Nilvero/SysWbud1/src/MainMenu.h

/*
 * MainMenu.h
 *
 *  Created on: May 6, 2016
 *      Author: krzys
 */
#include "stm32f429i_discovery_lcd.h"
#include "Button.h"
#include "stm32f429i_discovery_ioe.h"
#include "Chart.h"
#include "ChartsMenu.h"
#include "Results.h"

#ifndef MAINMENU_H_
#define MAINMENU_H_

void LCDinit(void);

void MainMenu();

#endif /* MAINMENU_H_ */
