Nilvero/SysWbud1/src/DS1337.c

/*
 * DS1337.c
 *
 *  Created on: Apr 30, 2016
 *      Author: krzys
 */
#include "DS1337.h"
#include "SharedFunctions.h"

void ds1337_INIT(){
	if(I2C3_CONFIGURED==0){
		InitI2C2();
	}
}
void ds1337_writeRecordToRegister(uint8_t adress,uint8_t value){
	// enable auto-ACK
	I2C_AcknowledgeConfig(I2C2,ENABLE);
	I2C_GenerateSTOP(I2C2,DISABLE);

	// generate start condition
	I2C_GenerateSTART(I2C2,ENABLE);
	while(!I2C_CheckEvent(I2C2,I2C_EVENT_MASTER_MODE_SELECT)){}

	// sent RTC adress
	I2C_Send7bitAddress(I2C2,DS1337_ADRESS<<1,I2C_Direction_Transmitter);
	while(!I2C_CheckEvent(I2C2,I2C_EVENT_MASTER_TRANSMITTER_MODE_SELECTED)){}

	// sent register ID adress
	I2C_SendData(I2C2,adress);
	while(I2C_CheckEvent(I2C2,I2C_EVENT_MASTER_BYTE_TRANSMITTING)!=SUCCESS){}

	// sent data to selected register
	I2C_SendData(I2C2,value);
	while(I2C_CheckEvent(I2C2,I2C_EVENT_MASTER_BYTE_TRANSMITTING)!=SUCCESS){}
	I2C_GenerateSTOP(I2C2,ENABLE);

}

void ds1337_writeRecordsToRegisters(uint8_t beginAdress,uint8_t * array,uint8_t size){
	// enable auto-ACK
	I2C_AcknowledgeConfig(I2C2,ENABLE);
	I2C_GenerateSTOP(I2C2,DISABLE);

	// generate start condition
	I2C_GenerateSTART(I2C2,ENABLE);
	while(!I2C_CheckEvent(I2C2,I2C_EVENT_MASTER_MODE_SELECT)){}

	// sent RTC adress
	I2C_Send7bitAddress(I2C2,DS1337_ADRESS<<1,I2C_Direction_Transmitter);
	while(!I2C_CheckEvent(I2C2,I2C_EVENT_MASTER_TRANSMITTER_MODE_SELECTED)){}

	// sent begin ID of writing register (auto-increment as default)
	I2C_SendData(I2C2,beginAdress);
	while(I2C_CheckEvent(I2C2,I2C_EVENT_MASTER_BYTE_TRANSMITTING)!=SUCCESS){}

	// write buffer to RTC
	uint8_t loopCounter=0;
	for(;loopCounter<size;loopCounter++){
		I2C_SendData(I2C2,array[loopCounter]);
		while(I2C_CheckEvent(I2C2,I2C_EVENT_MASTER_BYTE_TRANSMITTING)!=SUCCESS){}
	}
	// generate STOP condition
	I2C_GenerateSTOP(I2C2,ENABLE);
}

void ds1337_readRecordsFromRegisters(uint8_t beginAdress,uint8_t * array,uint8_t size){
	// wait for free line
	while(I2C_GetFlagStatus(I2C2, I2C_FLAG_BUSY)){}

	// generate start condition
	I2C_GenerateSTART(I2C2,ENABLE);
	while(!I2C_CheckEvent(I2C2,I2C_EVENT_MASTER_MODE_SELECT)){}

	// sent RTC adress
	I2C_Send7bitAddress(I2C2,DS1337_ADRESS<<1,I2C_Direction_Transmitter);
	while(!I2C_CheckEvent(I2C2,I2C_EVENT_MASTER_TRANSMITTER_MODE_SELECTED)){}

	// sent adress of first first reading register (auto-increment as default)
	I2C_SendData(I2C2,beginAdress);
	while(I2C_CheckEvent(I2C2,I2C_EVENT_MASTER_BYTE_TRANSMITTING)!=SUCCESS){}

	// generate stop
	I2C_GenerateSTART(I2C2,ENABLE);
	while(I2C_CheckEvent(I2C2,I2C_EVENT_MASTER_MODE_SELECT)!=SUCCESS){}

	// enable auto-acknowledge
	I2C_AcknowledgeConfig(I2C2,ENABLE);
	I2C_GenerateSTOP(I2C2,DISABLE);

	// sent RTC adress
	I2C_Send7bitAddress(I2C2,DS1337_ADRESS<<1,I2C_Direction_Receiver);
	while(I2C_CheckEvent(I2C2,I2C_EVENT_MASTER_RECEIVER_MODE_SELECTED)!=SUCCESS){}

	// read selected number of registers
	uint8_t loopCounter=0;
	for(;loopCounter<size;loopCounter++){
		// if only one remain disable ACK and prepare to generate stop condition
		if(loopCounter==(size-1)){
			I2C_AcknowledgeConfig(I2C2,DISABLE);
			I2C_GenerateSTOP(I2C2,ENABLE);
		}

		while(I2C_CheckEvent(I2C2,I2C_EVENT_MASTER_BYTE_RECEIVED)!=SUCCESS){}
		array[loopCounter]=I2C_ReceiveData(I2C2);
	}
}

void ds1337_readRecordsFromRegister(uint8_t adress,uint8_t * ptrToBuffer){
	// generate start condition
	I2C_GenerateSTART(I2C2,ENABLE);
	while(!I2C_CheckEvent(I2C2,I2C_EVENT_MASTER_MODE_SELECT)){}

	// sent RTC adress
	I2C_Send7bitAddress(I2C2,DS1337_ADRESS<<1,I2C_Direction_Transmitter);
	while(!I2C_CheckEvent(I2C2,I2C_EVENT_MASTER_TRANSMITTER_MODE_SELECTED)){}

	// sent reading register ID
	I2C_SendData(I2C2,adress);
	while(I2C_CheckEvent(I2C2,I2C_EVENT_MASTER_BYTE_TRANSMITTING)!=SUCCESS){}

	// generate start condition
	I2C_GenerateSTART(I2C2,ENABLE);
	while(I2C_CheckEvent(I2C2,I2C_EVENT_MASTER_MODE_SELECT)!=SUCCESS){}

	// sent RTC adress
	I2C_Send7bitAddress(I2C2,DS1337_ADRESS<<1,I2C_Direction_Receiver);
	while(I2C_CheckEvent(I2C2,I2C_EVENT_MASTER_RECEIVER_MODE_SELECTED)!=SUCCESS){}

	// disable auto-ack and eneble generating stop condition after receiving data
	I2C_AcknowledgeConfig(I2C2,DISABLE);
	I2C_GenerateSTOP(I2C2,ENABLE);

	// read register to buffer
	while(I2C_CheckEvent(I2C2,I2C_EVENT_MASTER_BYTE_RECEIVED)!=SUCCESS){}
	*ptrToBuffer=I2C_ReceiveData(I2C2);
}
void ds1337_writeTimeStructure(){
	uint8_t buffer[7];

	// convert integers to BDC format using by RTC
	buffer[0]=((DS1337_TIME.seconds/10)<<4)|(DS1337_TIME.seconds%10);
	buffer[1]=((DS1337_TIME.minutes/10)<<4)|(DS1337_TIME.minutes%10);
	buffer[2]=((DS1337_TIME.hour/10)<<4)|(DS1337_TIME.hour%10);
	buffer[3]=DS1337_TIME.day;
	buffer[4]=((DS1337_TIME.month/10)<<4)|(DS1337_TIME.month%10);
	buffer[5]=((DS1337_TIME.date/10)<<4)|(DS1337_TIME.date%10);
	buffer[6]=((DS1337_TIME.decade/10)<<4)|(DS1337_TIME.decade%10);

	// save buffer to RTC
	ds1337_writeRecordsToRegisters(DS1337_BEGIN_OF_TIME_REGISTER,buffer,7);
}

void ds1337_readTimeStructure(){
	uint8_t buffer[7];

	// read RTC time registers to buffer
	ds1337_readRecordsFromRegisters(DS1337_BEGIN_OF_TIME_REGISTER,buffer,7);

	// convert values from buffer (BDC code) to integers
	DS1337_TIME.seconds=(buffer[0]&(0b00001111))+((buffer[0]>>4)&0b00000111)*10;
	DS1337_TIME.minutes=(buffer[1]&(0b00001111))+((buffer[1]>>4)&0b00000111)*10;
	DS1337_TIME.hour=(buffer[2]&(0b00001111))+((buffer[2]>>4)&0b00000011)*10;
	DS1337_TIME.day=buffer[3]&0b00000111;
	DS1337_TIME.date=(buffer[4]&(0b00001111))+((buffer[4]>>4)&0b00000011)*10;
	DS1337_TIME.month=(buffer[5]&(0b00001111))+((buffer[5]>>4)&0b00000001)*10;
	DS1337_TIME.decade=(buffer[6]&(0b00001111))+((buffer[6]>>4)&0b00001111)*10;
}
