Nilvero/SysWbud1/src/ChartsMenu.h

/*
 * ChartsMenu.h
 *
 *  Created on: May 6, 2016
 *      Author: krzys
 */

#ifndef CHARTSMENU_H_
#define CHARTSMENU_H_
#include "stm32f429i_discovery_ioe.h"
#include "Button.h"
#include "Results.h"
#include "ChartPanel.h"
#include "SharedFunctions.h"
void ChartsMenu();

#endif /* CHARTSMENU_H_ */
