Nilvero/SysWbud1/src/SEN0159.h

/*
 * SEN0159.H
 *
 *  Created on: May 27, 2016
 *      Author: krzys
 */

#ifndef SEN0159_H_
#define SEN0159_H_

#include "stm32f4xx_gpio.h"
#include "stm32f4xx_tim.h"
#include "stm32f4xx_adc.h"

void SEN0159init();
int SEN0159Result();
#endif /* SEN0159_H_ */
